Tomsei/NXPCup-2025/HW/3D models/3mf/Halterung_Kameramast_clip_Neu.3mf

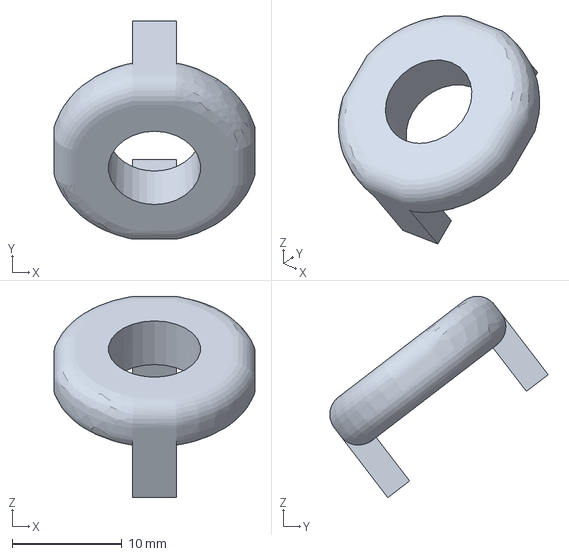
[picture p15: CAD file, 2025-04-10]
HW/3D models/3mf/Halterung_Kameramast_clip_Neu.3mf
18.3 x 19.9 x 18.3 mm
