Tomsei/NXPCup-2025/HW/3D models/Freecad/Halterung_Platine_Vorne.FCStd

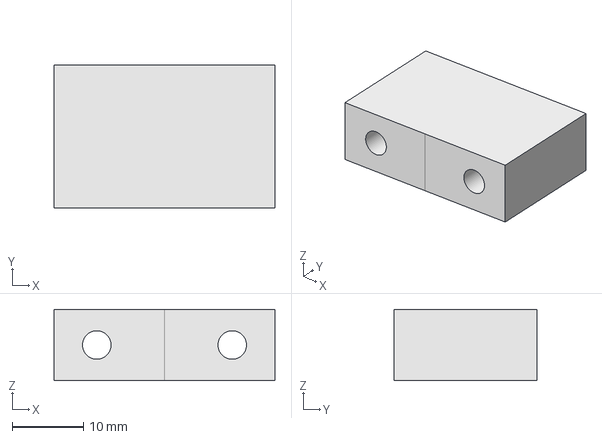
[picture p16: CAD file, 2025-04-10]
HW/3D models/Freecad/Halterung_Platine_Vorne.FCStd
31.0 x 20.0 x 10.0 mm
