Tomsei/NXPCup-2025/HW/3D models/3mf/Gussformen_Gesamt.3mf

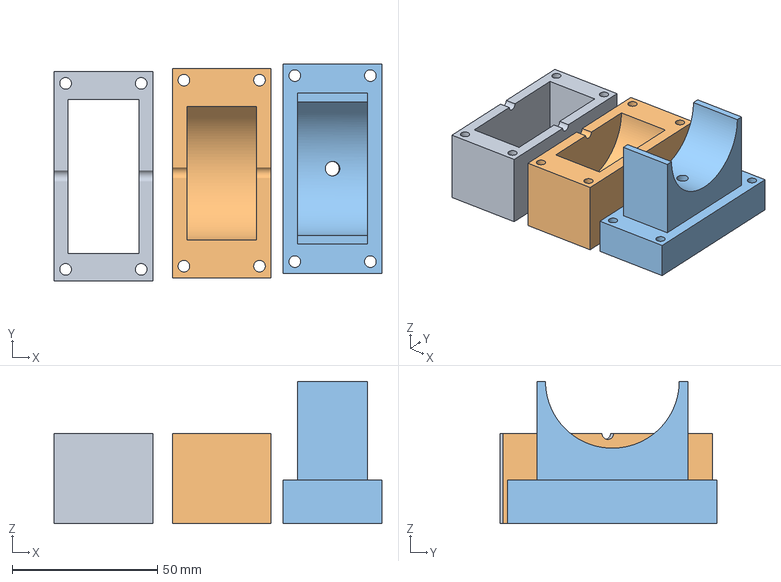
[picture p17: CAD file, 2025-04-10]
HW/3D models/3mf/Gussformen_Gesamt.3mf
112.9 x 74.7 x 49.0 mm
