Tomsei/NXPCup-2025/HW/3D models/Freecad/Halterung_Kameramast_alt.FCStd

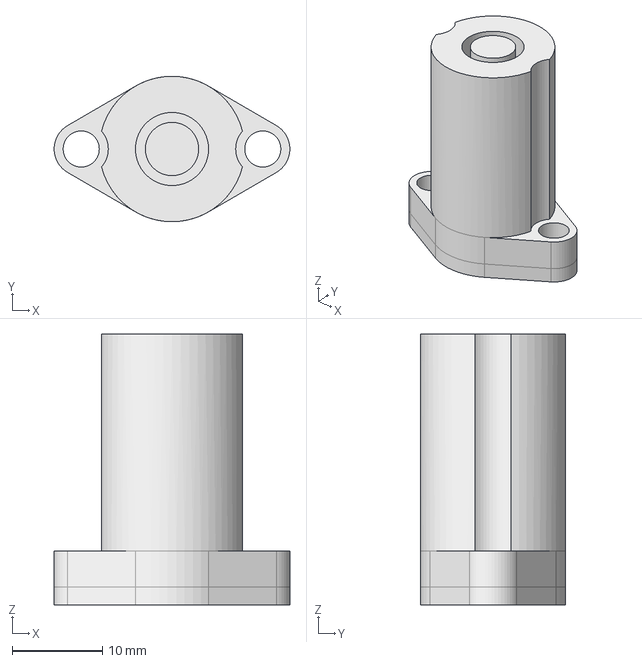
[picture p18: CAD file, 2025-04-10]
HW/3D models/Freecad/Halterung_Kameramast_alt.FCStd
26.1 x 16.1 x 30.0 mm
