Tomsei/NXPCup-2025/HW/3D models/Freecad/Halterung_Display.FCStd

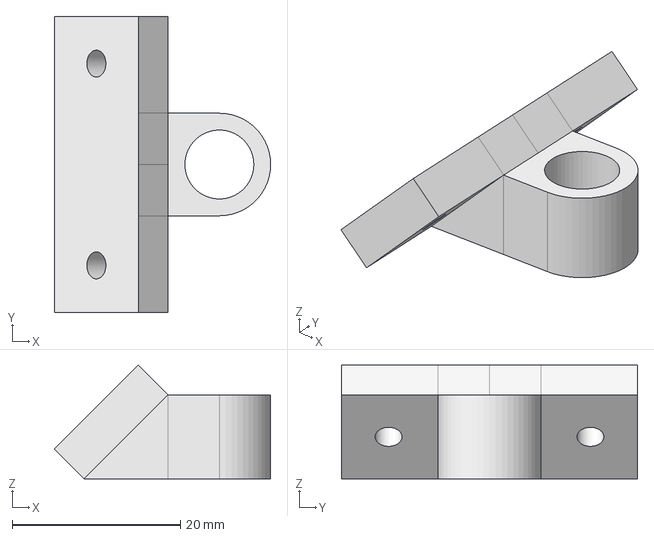
[picture p19: CAD file, 2025-04-10]
HW/3D models/Freecad/Halterung_Display.FCStd
25.7 x 35.2 x 13.5 mm
