Tomsei/NXPCup-2025/HW/3D models/Freecad/Halterung_Platine_Mitte.FCStd

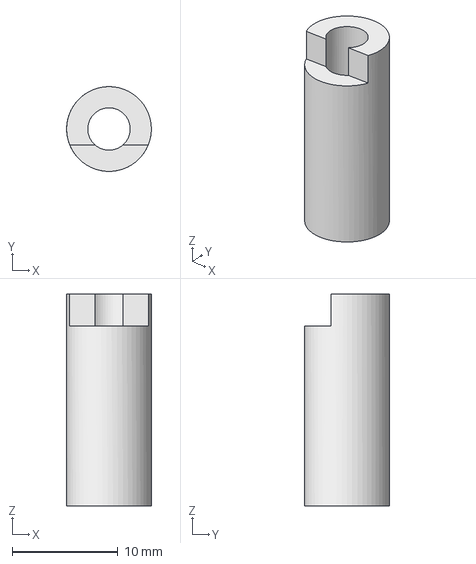
[picture p20: CAD file, 2025-04-10]
HW/3D models/Freecad/Halterung_Platine_Mitte.FCStd
8.00 x 8.00 x 20.0 mm
