Tomsei/NXPCup-2025/HW/3D models/Freecad/Halterung_Motor.FCStd

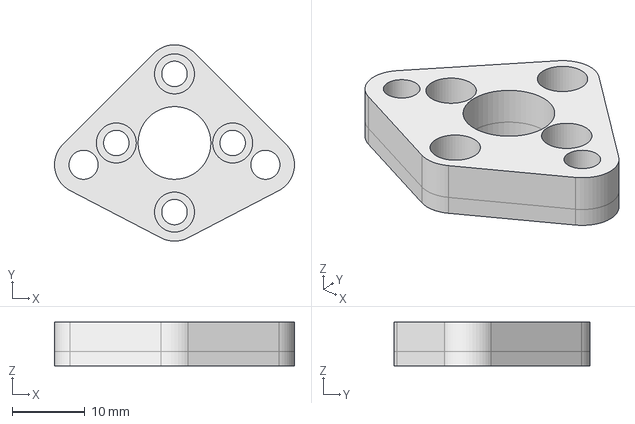
[picture p21: CAD file, 2025-04-10]
HW/3D models/Freecad/Halterung_Motor.FCStd
33.0 x 27.0 x 6.00 mm
