Tomsei/NXPCup-2025/HW/3D models/Freecad/Halterung_ToF_Distanzsensor.FCStd

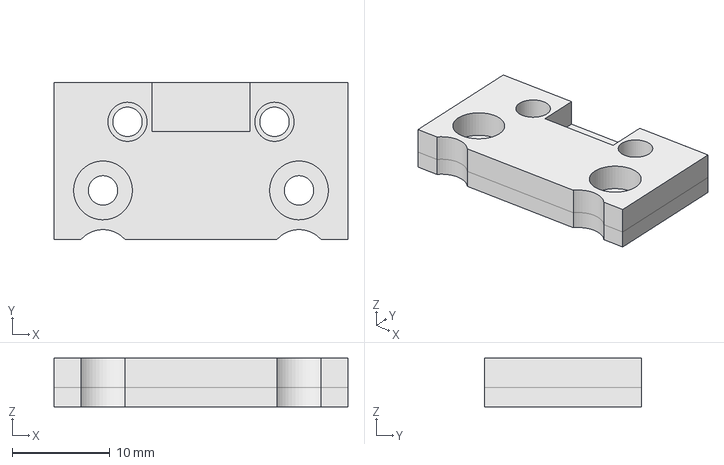
[picture p22: CAD file, 2025-04-10]
HW/3D models/Freecad/Halterung_ToF_Distanzsensor.FCStd
30.0 x 16.0 x 5.00 mm
