Tomsei/NXPCup-2025/HW/3D models/Freecad/Halterung_Kamera_Neu.FCStd

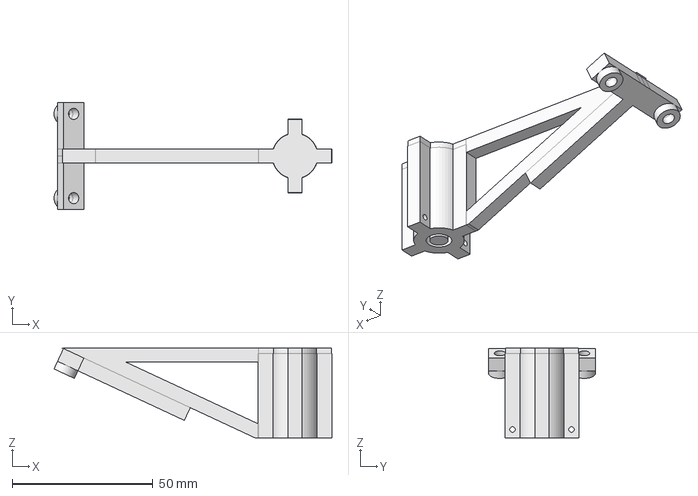
[picture p23: CAD file, 2025-04-10]
HW/3D models/Freecad/Halterung_Kamera_Neu.FCStd
98.9 x 38.0 x 32.0 mm
