Tomsei/NXPCup-2025/HW/3D models/Freecad/Radhalterung.FCStd

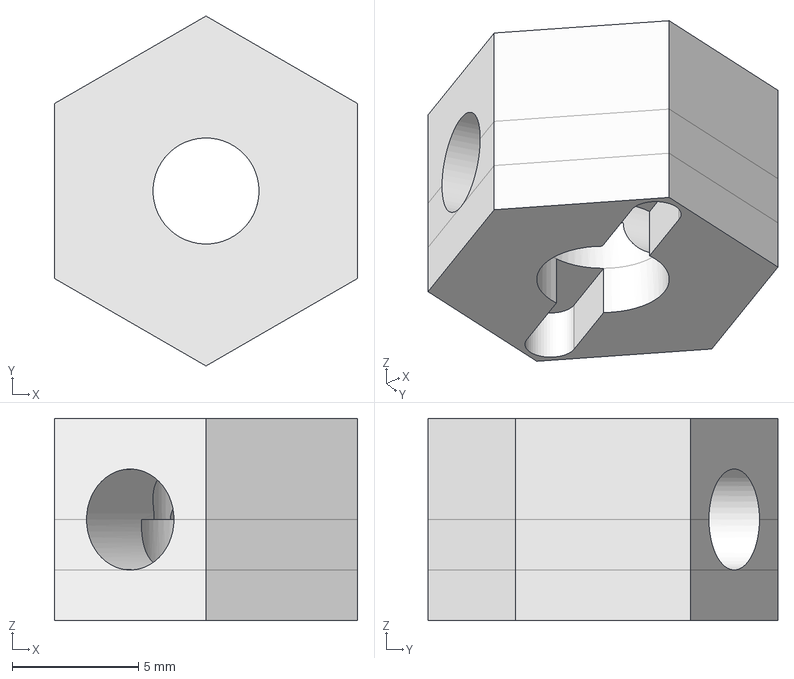
[picture p24: CAD file, 2025-04-10]
HW/3D models/Freecad/Radhalterung.FCStd
12.0 x 13.9 x 8.00 mm
