Tomsei/NXPCup-2025/HW/3D models/Freecad/Halterung_Optical_Flow.FCStd

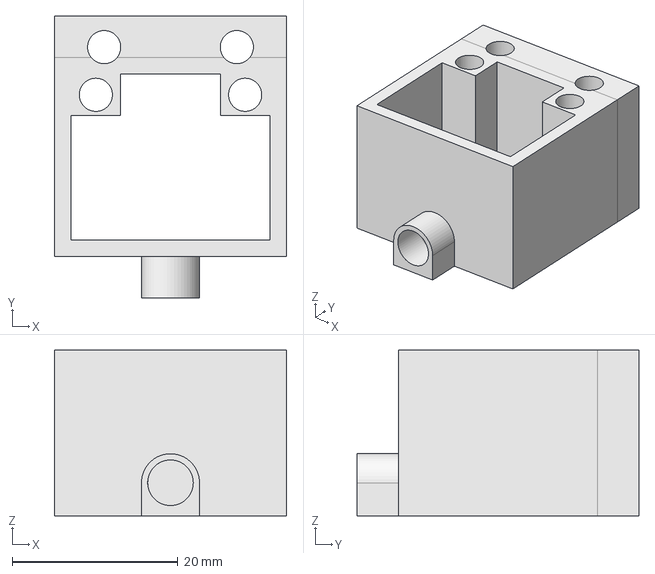
[picture p25: CAD file, 2025-04-10]
HW/3D models/Freecad/Halterung_Optical_Flow.FCStd
28.0 x 34.0 x 20.0 mm
