Tomsei/NXPCup-2025/HW/3D models/Freecad/Halterung_Kamera_alt.FCStd

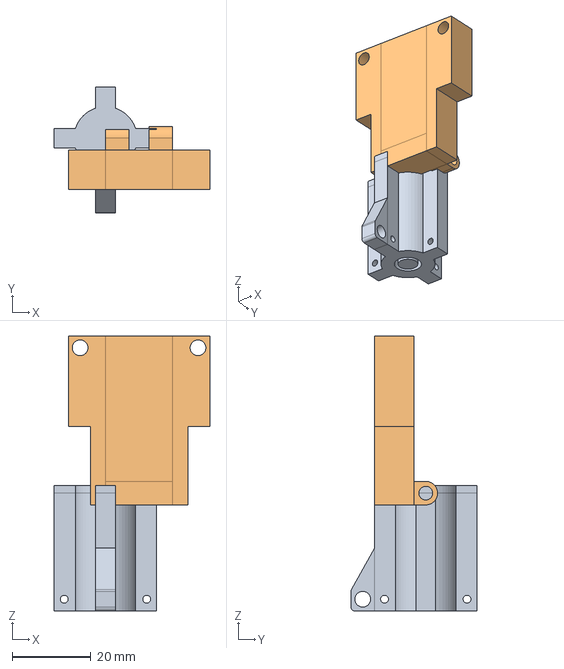
[picture p26: CAD file, 2025-04-10]
HW/3D models/Freecad/Halterung_Kamera_alt.FCStd
39.6 x 32.1 x 70.0 mm
Körper
Körper001
