Tomsei/NXPCup-2025/HW/3D models/Freecad/Halterung_Relais_Spannungswandler.FCStd

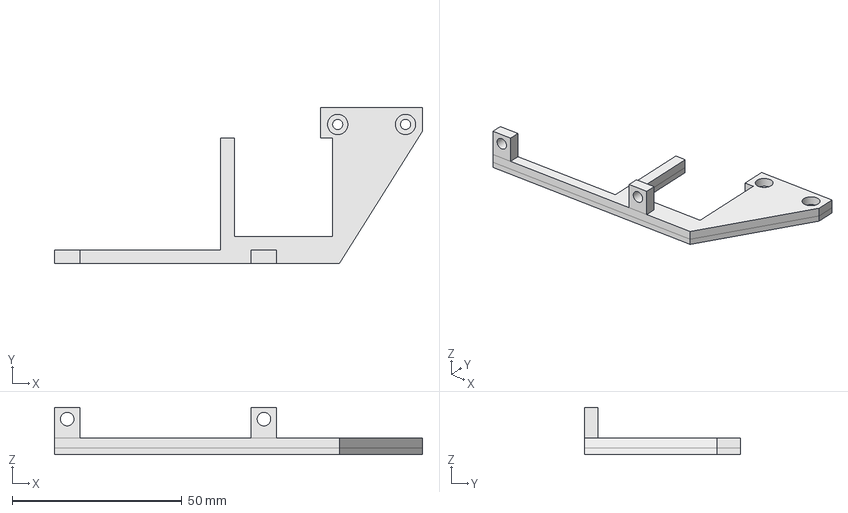
[picture p27: CAD file, 2025-04-10]
HW/3D models/Freecad/Halterung_Relais_Spannungswandler.FCStd
108.5 x 46.0 x 14.0 mm
