Tomsei/NXPCup-2025/SW/SW-Kit/PlatformIO/src/configuration/globalConfig.h

/**
 * Global Configuration - defines 
 * 
 * all global defines of the programm. 
 * - the definition of the used pins
 *  
 * @author Tom Seiffert
 */


/* ----- pin definitions -----  */
#define MOTOR_ESC_PIN 29 //
#define SERVO_PIN 28
#define CAM_SPI_MISO 12

//spi definition
#define SPI_BUFFER_SIZE 100
