Tomsei/NXPCup-2025/SW/PlatformIO/src/singleComponents/irObstacleDetection_ARD_LINEFINDER.cpp

/**
 * Single component - ir obstacle detection definition
 * 
 * Basic code to test the function of the ard line finder
 * Read and print the data of both sensors
 * 
 * @author Tom Seiffert
 */
#include "configuration/globalConfig.h"

#ifdef SINGLE_COMPONENTS_TEST

//Source: https://cdn-reichelt.de/documents/datenblatt/A300/SEN-KY032-ANLEITUNG.pdf
#include <Arduino.h>

namespace SingleComponent {

    /**
     * setup the ard line finder 
     */
    void setupArdLinefinder() {
        pinMode(ARD_LINE_FINDER1, INPUT);
        pinMode(ARD_LINE_FINDER2, INPUT);
    }

    bool blackSensor1 = false;
    bool blackSensor2 = false;

    /**
     * method to read the values of ard line finder and print if a change is detected
     */
    void runArdLineFinder() {
        bool valSensor1 = digitalRead(ARD_LINE_FINDER1);
        bool valSensor2 = digitalRead(ARD_LINE_FINDER2);

        if (valSensor1 == HIGH && blackSensor1) {
            CONSOLE.println("ARD Linefinder 1: Black to White");
            blackSensor1 = false;
        } else if (valSensor1 == LOW && !blackSensor1) {
            CONSOLE.println("ARD Linefinder 1: White to Black");
            blackSensor1 = true;
        }

        if (valSensor2 == HIGH && blackSensor2) {
            CONSOLE.println("ARD Linefinder 2: Black to White");
            blackSensor2 = false;
        } else if (valSensor2 == LOW && !blackSensor2) {
            CONSOLE.println("ARD Linefinder 2: White to Black");
            blackSensor2 = true;
        }
    }
}
#endif
