Tomsei/NXPCup-2025/SW/PlatformIO/src/singleComponents/poti.cpp

/**
 * Single component - poti definition
 * 
 * Basic code to test the function of the poti 
 * Read and print the poti value
 * 
 * @author Tom Seiffert
 */
#include "configuration/globalConfig.h"

#ifdef SINGLE_COMPONENTS_TEST

#include <Arduino.h>

namespace SingleComponent {
    
    //no setup needed
    void setupPoti() {
        return;
    }

    /**
     * method to call in loop to print poti values
     */
    void runPoti() {
        int poti1 = analogRead(POTI1);
        int poti2 = analogRead(POTI2);
        if(poti1 > 500 || poti2 > 500) {
            CONSOLE.print("Poti 1: "); CONSOLE.print(poti1);
            CONSOLE.print("\t Poti 2: "); CONSOLE.println(poti2);
        }
    }
}
#endif
