Tomsei/NXPCup-2025/SW/PlatformIO/src/singleComponents/teensy.cpp

/**
 * Single component - teensy definition
 * 
 * Basic code to test the teensy
 * Just make the teensy blink
 * 
 * @author Tom Seiffert
 */
#include "configuration/globalConfig.h"

#ifdef SINGLE_COMPONENTS_TEST

#include <Arduino.h>

namespace SingleComponent {

    /**
     * setup for teensy blink
     */
    void setupTeensyBlink() {
        pinMode(ON_BOARD_LED, OUTPUT);
    }
    /**
     * teensy test blink
     */
    void teensyBlink() {
        digitalWrite(ON_BOARD_LED, HIGH);
        delay(1000);
        digitalWrite(ON_BOARD_LED, LOW);
        delay(1000);   
    }
}
#endif
